FarelMP/Temperature-Control-Project/File Program/TempControl/Core/Inc/system.h

/*
 * system.h
 *
 *  Created on: Dec 3, 2024
 *      Author: farelmp
 */

#ifndef INC_SYSTEM_H_
#define INC_SYSTEM_H_

#include "Calculation.h"
#include "Communication.h"

void systemFunction(void);
void systemTimer(void);
void systemVal(void);

#endif /* INC_SYSTEM_H_ */
